KetumKeton/Nixie-Tube-Driver-with-ESP8266/V1.1/Ekran görüntüsü 2025-02-23 164843.png

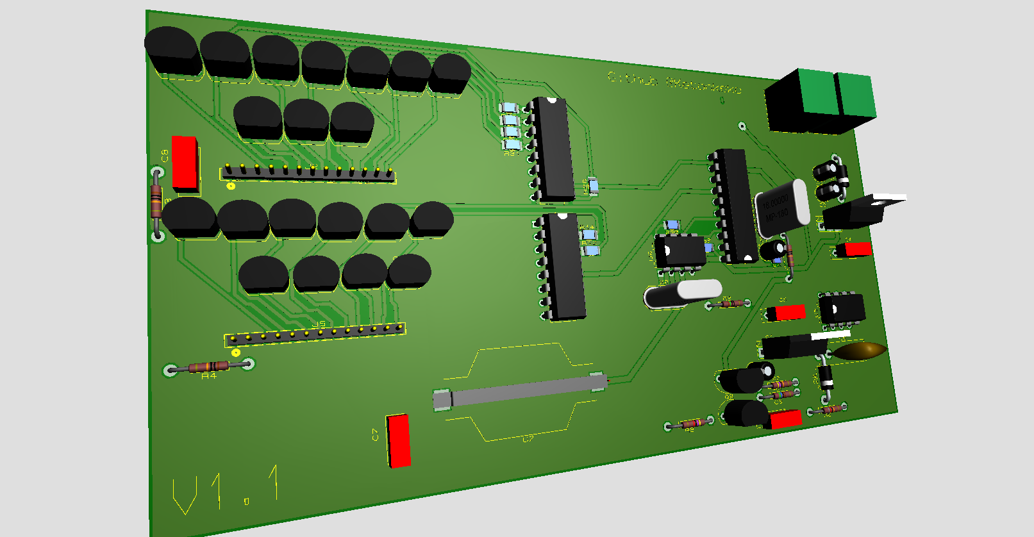
V1.1/Ekran görüntüsü 2025-02-23 164843.png
