KetumKeton/Nixie-Tube-Driver-with-ESP8266/V5.1-Community-Edition/5.1/nixie-clock-pcb-v5-1.png

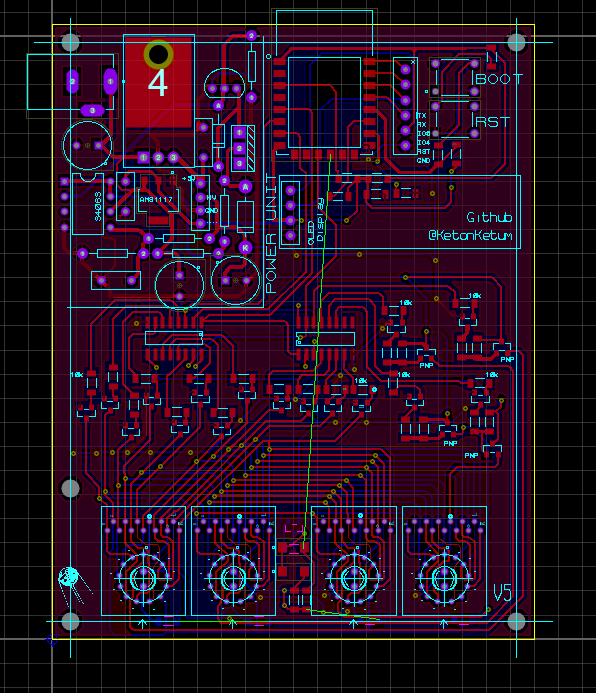
V5.1-Community-Edition/5.1/nixie-clock-pcb-v5-1.png
