KetumKeton/Nixie-Tube-Driver-with-ESP8266/V5.1-Community-Edition/5.1_PCB_Image.jpeg

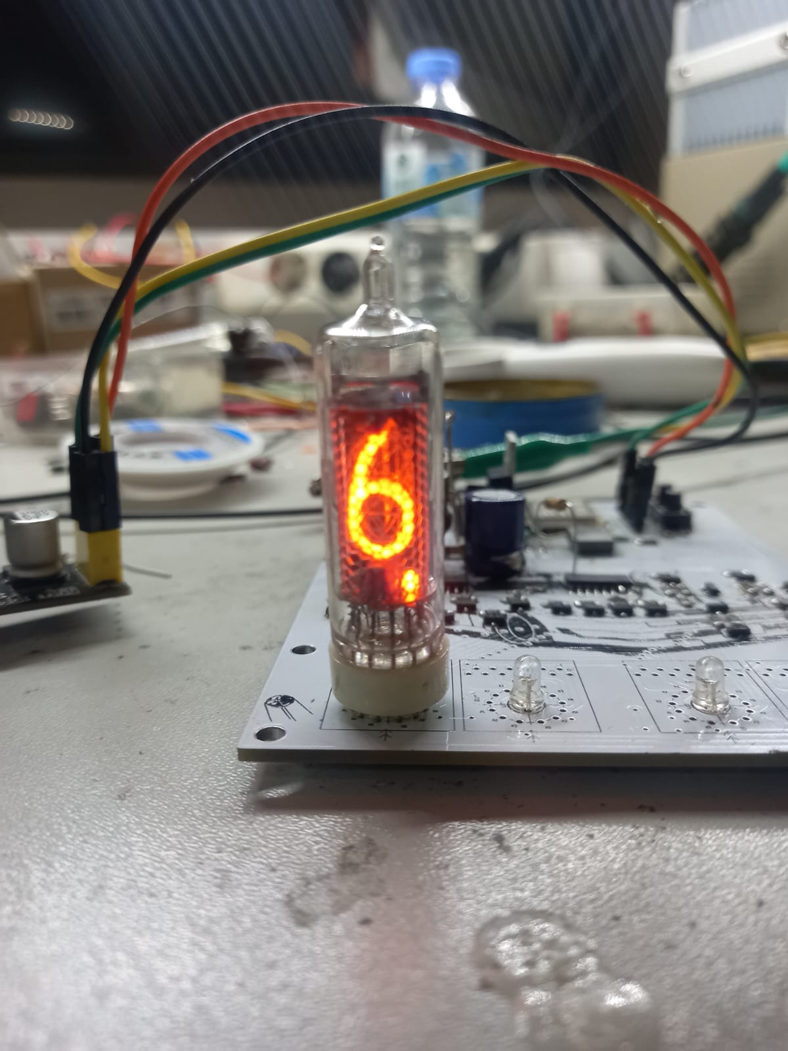
V5.1-Community-Edition/5.1_PCB_Image.jpeg
