KetumKeton/Nixie-Tube-Driver-with-ESP8266/V5.1-Community-Edition/HV-Power-Supply/12V-HV-V1-2-pcb.png

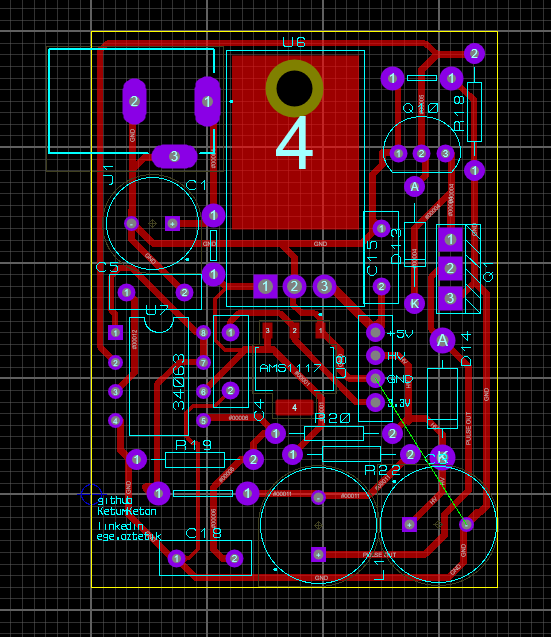
V5.1-Community-Edition/HV-Power-Supply/12V-HV-V1-2-pcb.png
