KetumKeton/Nixie-Tube-Driver-with-ESP8266/V6-Professional-Edition/NixieClock-V6-PCB.png

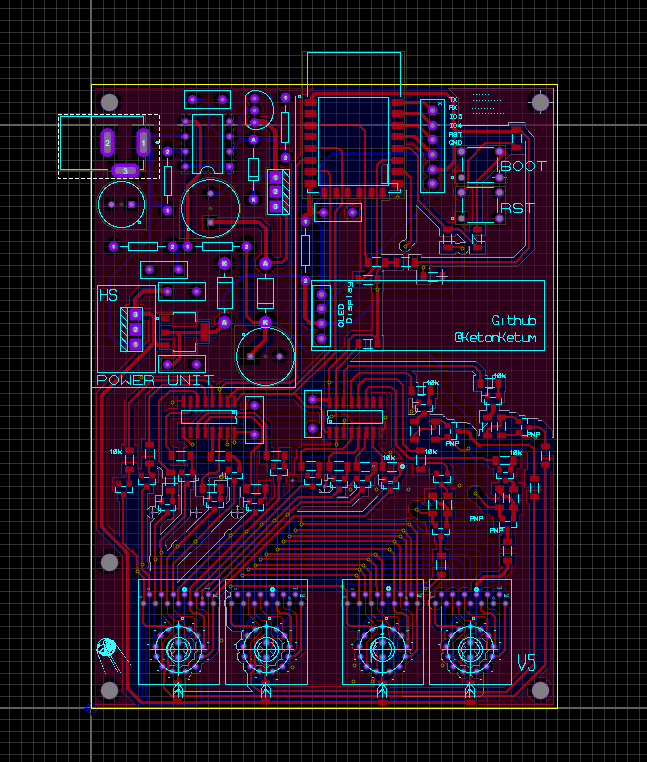
V6-Professional-Edition/NixieClock-V6-PCB.png
