KetumKeton/Nixie-Tube-Driver-with-ESP8266/V5.1-Community-Edition/IN-16-Tube-Test-IMAGE.jpg

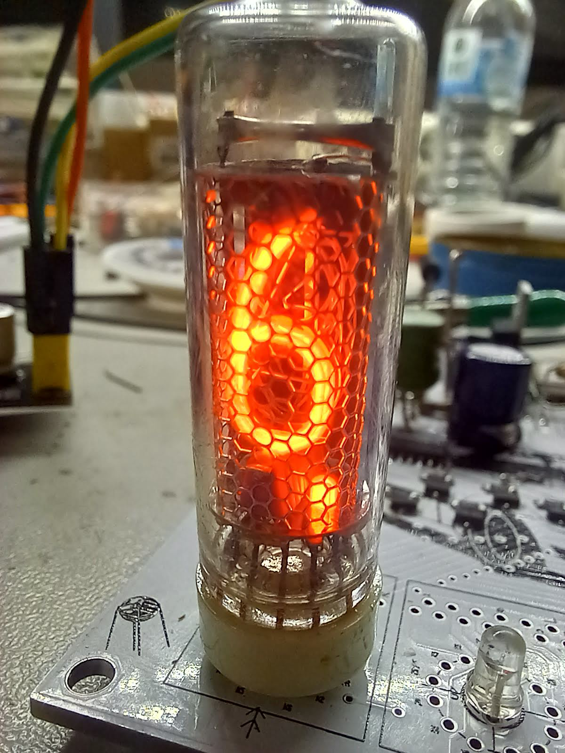
V5.1-Community-Edition/IN-16-Tube-Test-IMAGE.jpg
